EwoudVV/ducktop2/mechanical/layout-planner.html

ducktop2 floorplan

Select Pan Fit - + Save Export Import Reset Panel

Ready

## View

Grid mm Zoom

Snap to grid

Fit Base Fit Lid Fit All

## Selected

Name

X Y Zone

W H Kind

Focus Center H Center V Rotate -45 +45 Duplicate Delete Lock Hide

## Parts

Add Part Select All Clear Front Back

## JSON

Mouse wheel zooms at cursor. Drag empty space to box-select. Spacebar or Pan mode drags the view. Shift/Command-click adds to selection. White handles resize one unlocked part.

## Build Next

Keyboard rev A is now a real 273.5 x 80.0 mm MX ULP daughterboard. Its J320 connector is a Hirose FH12-30S-0.5SH(55), 30-pin 0.5 mm right-angle FFC. Use this planner to freeze the mainboard envelope, side/rear connector zones, thermal stack, battery clearances, display direct-eDP hinge route, recessed Ethernet jack, microphone opening, and cable paths before freezing the main PCB outline.
