EwoudVV/ducktop2/mechanical/case-prototype/viewer-template.html

# ducktop2 / case prototype

Actual CAD geometry. Drag to orbit, scroll to zoom. Editable parameters are in assembly.json.

closed105°180° opening 105° explodedtopsection sidereset view

cut at X off

unresolved fit checks

Framework Computer Inc hinge references: CC BY 4.0, revision 0 / 2023-06-27. STEP coordinates retain front +Y and use Z down; this view is rotated to show height upward.

loading geometry…
