EwoudVV/ducktop2/mechanical/case-prototype/mounting-schedule.csv

reference | X_mm | Y_mm | Z_mm | mating_part | hole_mm | thread | support_height_mm | fastener_length_mm | insulation | status | washer_thickness_mm | top_thread_engagement_mm | engagement_mm | head_diameter_mm | head_height_mm | OEM_screw_length_mm
center/H21 | 110.25 | 6.05 | -6.4 | base, nylon M2.5 male/female standoff | 2.7 | M2.5 | 4.0 | 5 | nylon screw, support, washer and underside nut; preserve PCB isolation | XY/drill verified from saved board; purchased hardware fit pending | 0.5 | 2.9
center/H22 | 105.0 | 70.0 | -6.4 | base, nylon M2.5 male/female standoff | 2.7 | M2.5 | 4.0 | 5 | nylon screw, support, washer and underside nut; preserve PCB isolation | XY/drill verified from saved board; purchased hardware fit pending | 0.5 | 2.9
center/H23 | 124.1 | 180.4 | -6.4 | base, nylon M2.5 male/female standoff | 2.7 | M2.5 | 4.0 | 5 | nylon screw, support, washer and underside nut; preserve PCB isolation | XY/drill verified from saved board; purchased hardware fit pending | 0.5 | 2.9
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
