EwoudVV/ducktop2/keyboard/images/layout.png

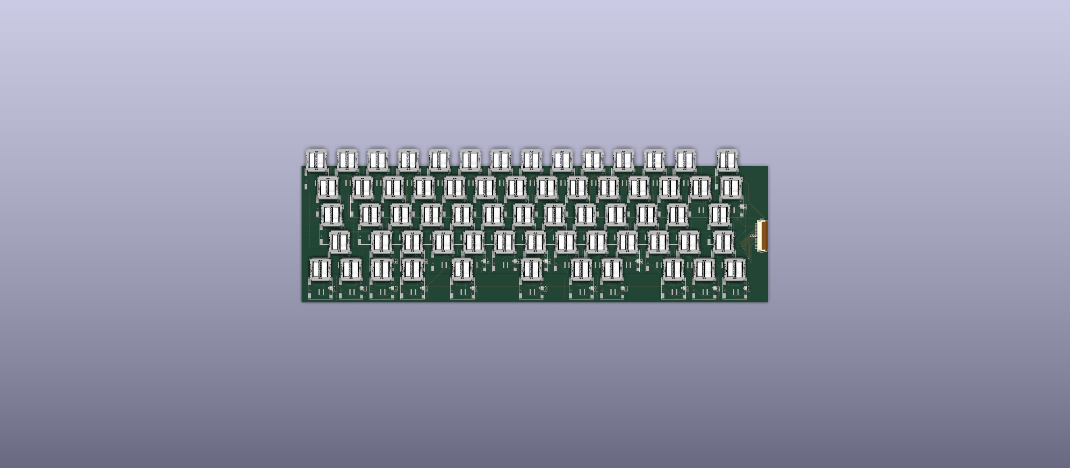
keyboard/images/layout.png
