EwoudVV/ducktop2/mechanical/case-prototype/views/closed.png

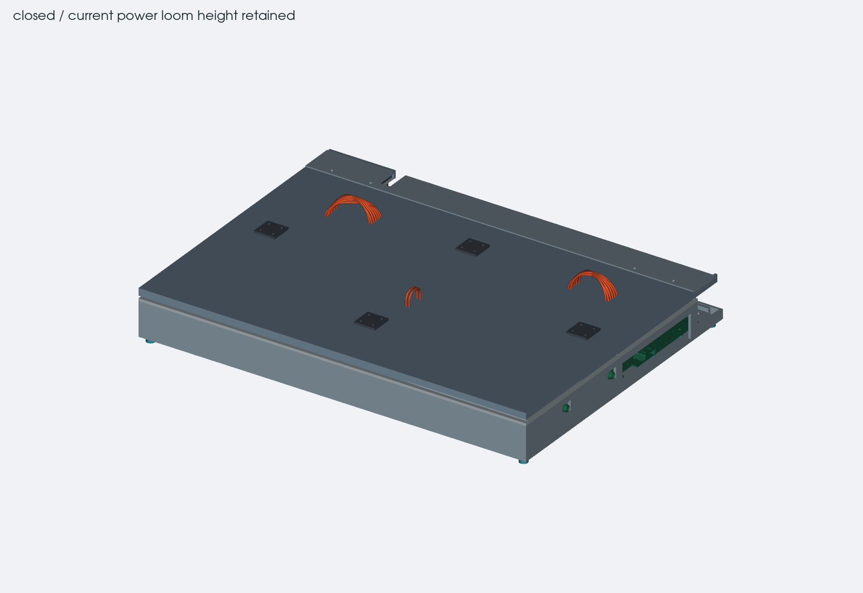
mechanical/case-prototype/views/closed.png
