EwoudVV/ducktop2/mechanical/case-prototype/views/cooling-section.png

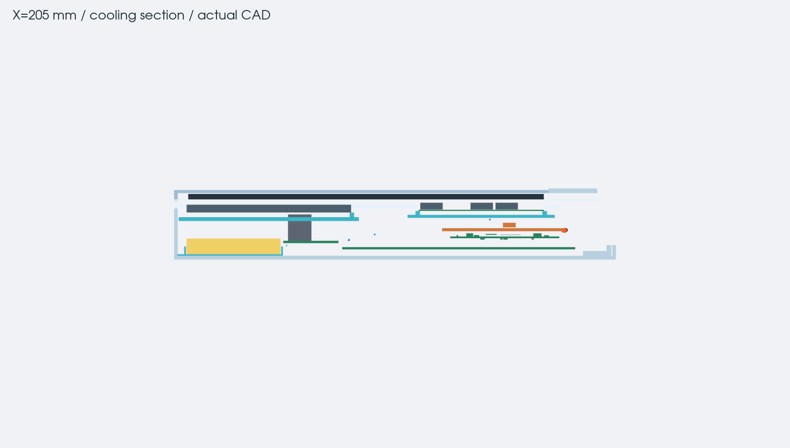
mechanical/case-prototype/views/cooling-section.png
