EwoudVV/ducktop2/mechanical/case-prototype/views/exploded.png

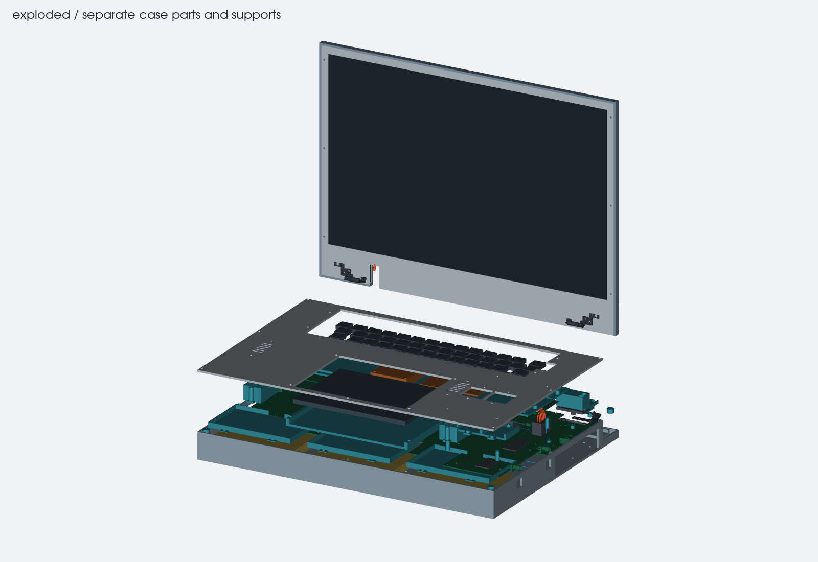
mechanical/case-prototype/views/exploded.png
