EwoudVV/ducktop2/mechanical/case-prototype/views/inside.png

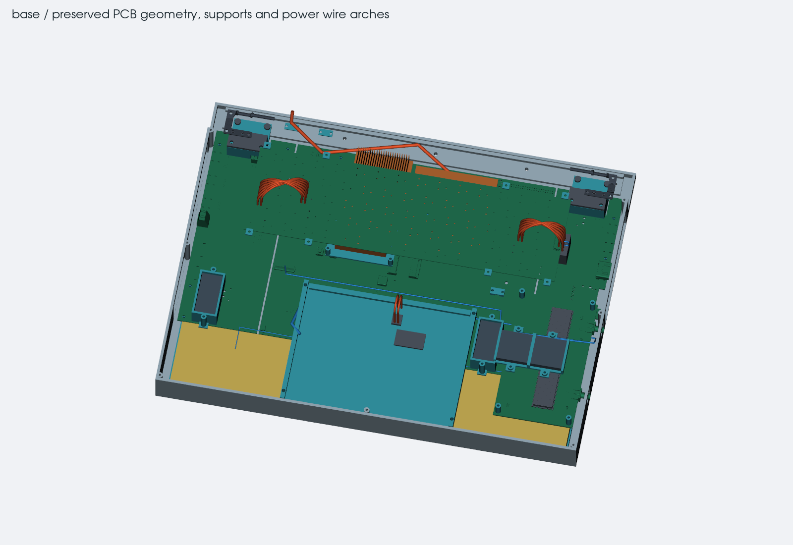
mechanical/case-prototype/views/inside.png
