EwoudVV/ducktop2/mechanical/power-harness.png

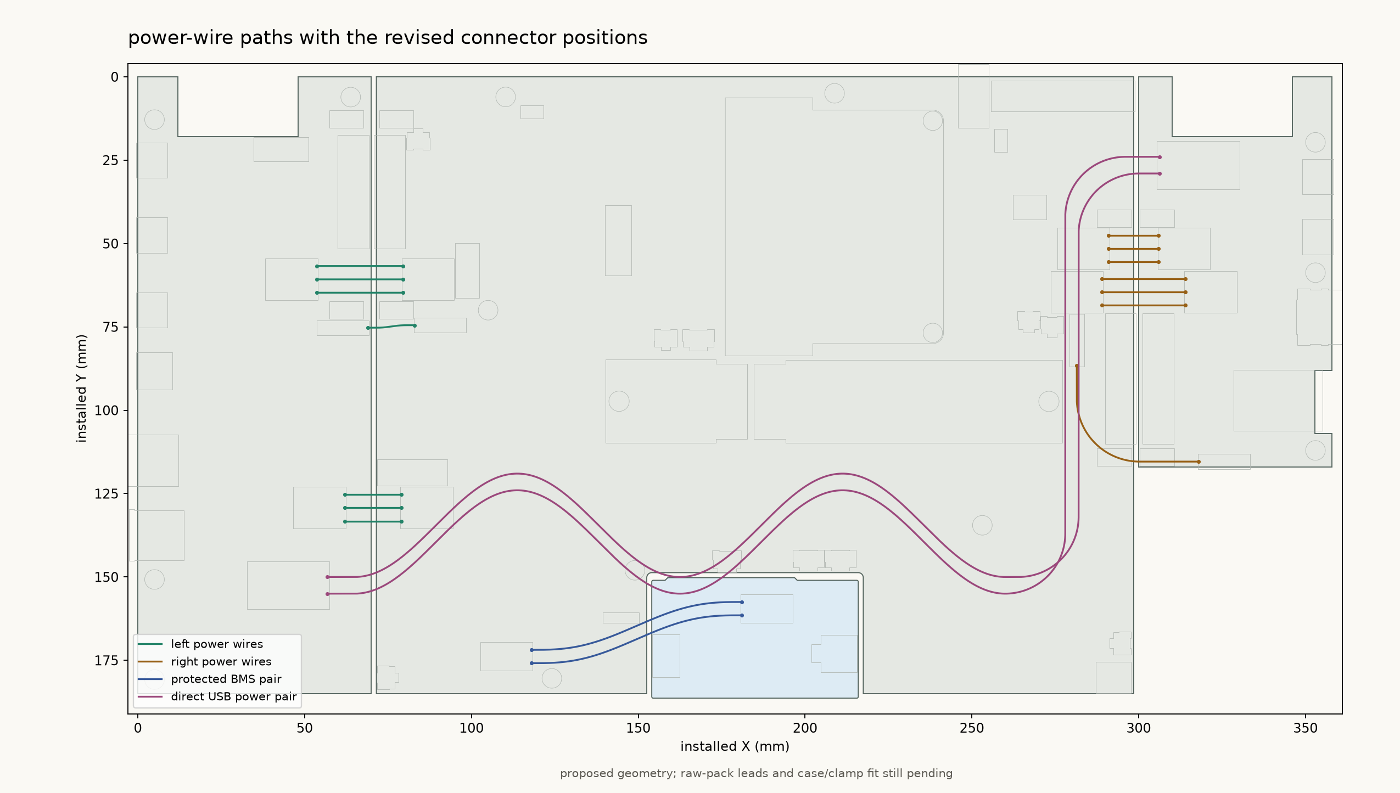
mechanical/power-harness.png
