EwoudVV/ducktop2/radio_daughterboard/images/iso.png

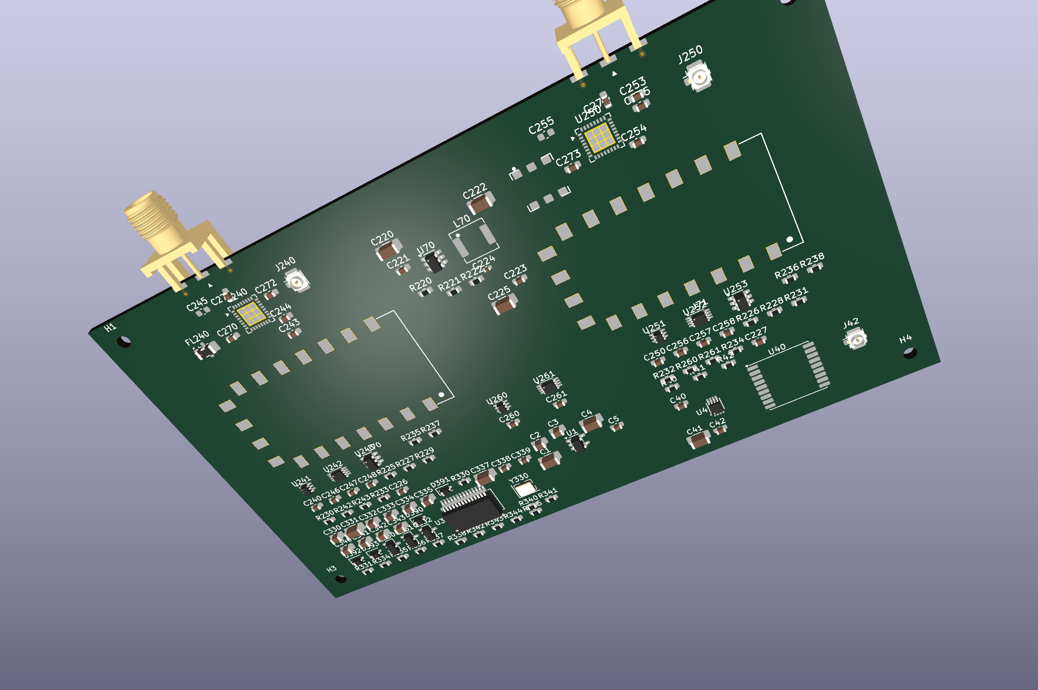
radio_daughterboard/images/iso.png
