EwoudVV/ducktop2/radio_daughterboard/images/top.png

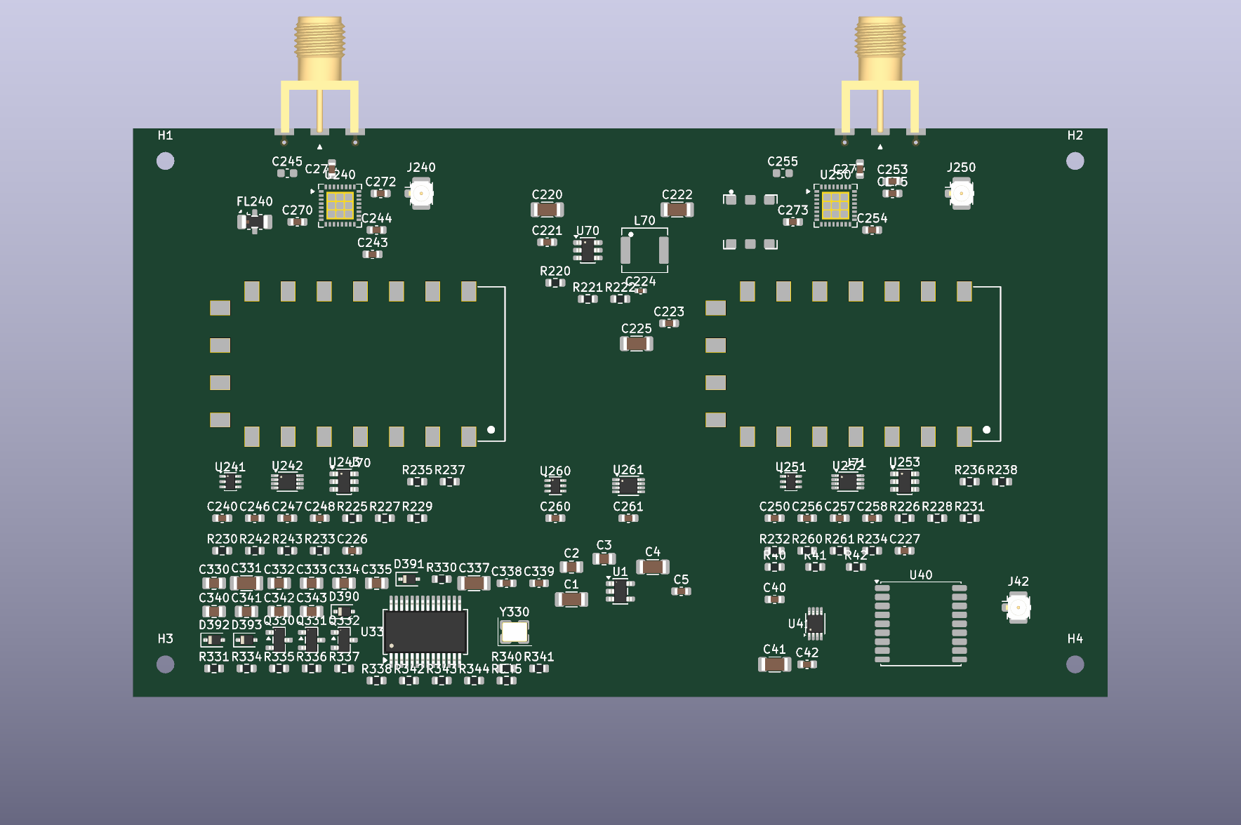
radio_daughterboard/images/top.png
