EwoudVV/ducktop2/mechanical/case-prototype/exports/hinge-tests/right-base-block.stl

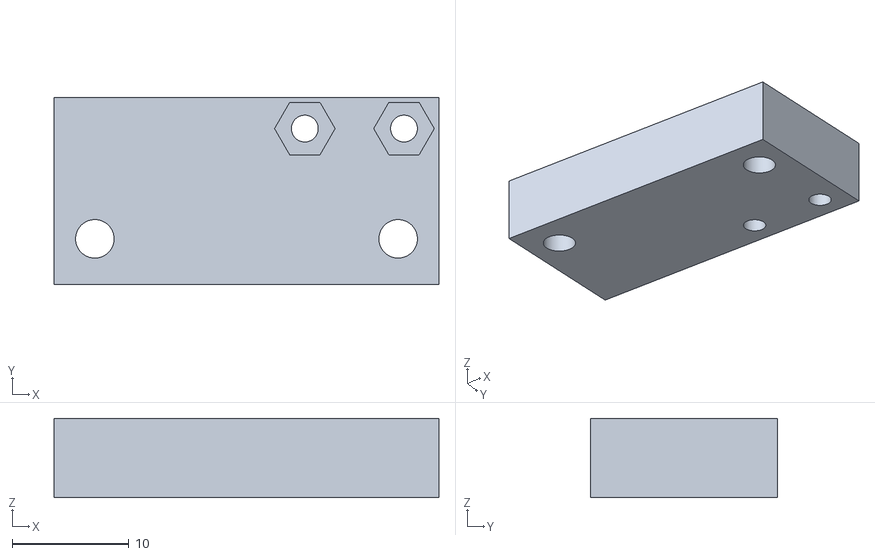
[picture p27: CAD file, 2026-09-26]
mechanical/case-prototype/exports/hinge-tests/right-base-block.stl
33.0 x 16.0 x 6.80
