EwoudVV/ducktop2/mechanical/case-prototype/exports/parts/right-lid-seat-2.step

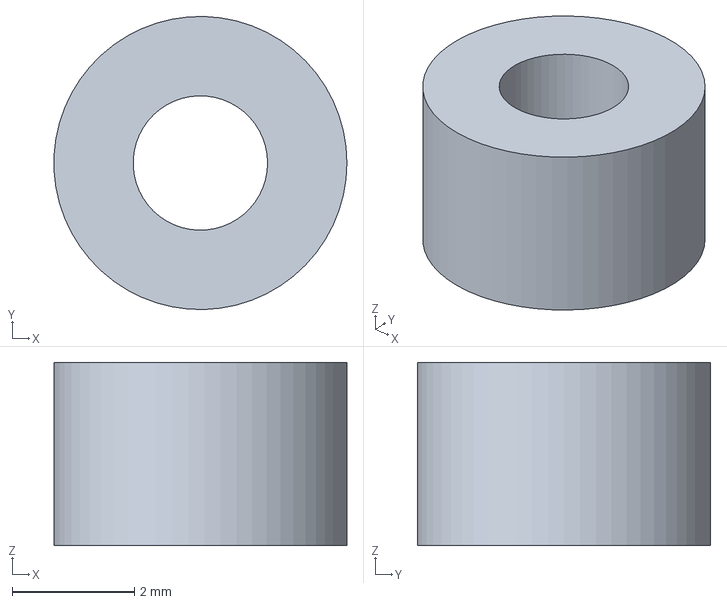
[picture p28: CAD file, 2026-09-26]
mechanical/case-prototype/exports/parts/right-lid-seat-2.step
4.80 x 4.80 x 3.00 mm
