EwoudVV/ducktop2/mechanical/case-prototype/exports/hinge-tests/left-base-block.stl

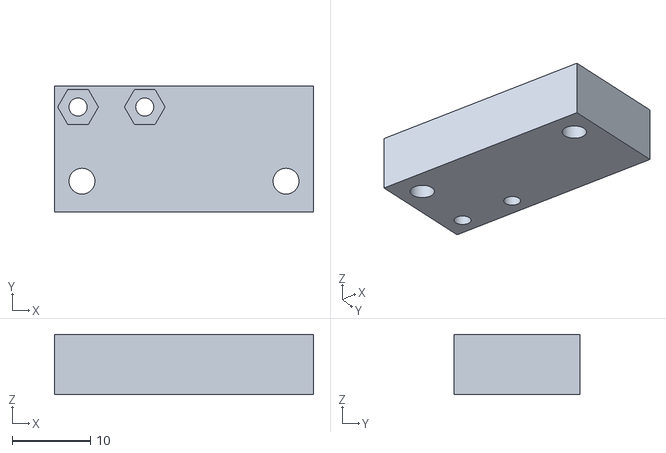
[picture p29: CAD file, 2026-09-26]
mechanical/case-prototype/exports/hinge-tests/left-base-block.stl
33.0 x 16.0 x 7.70
