EwoudVV/ducktop2/mechanical/case-prototype/exports/parts/cable-clamp-3.step

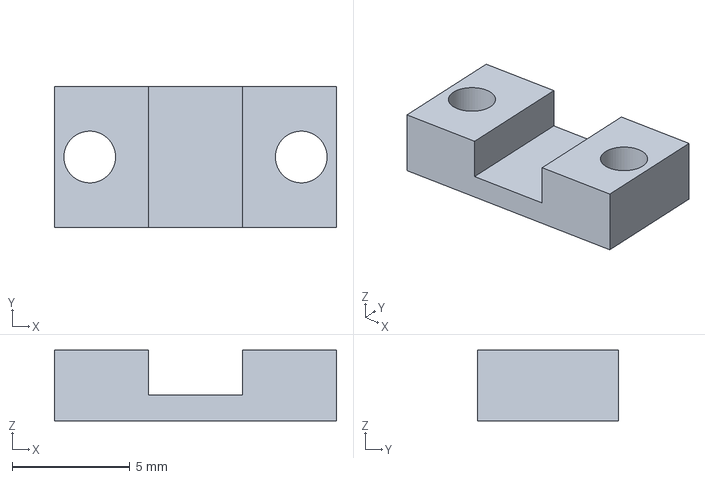
[picture p30: CAD file, 2026-09-26]
mechanical/case-prototype/exports/parts/cable-clamp-3.step
12.0 x 6.00 x 3.00 mm
