EwoudVV/ducktop2/mechanical/case-prototype/exports/parts/lid-shell-21.step

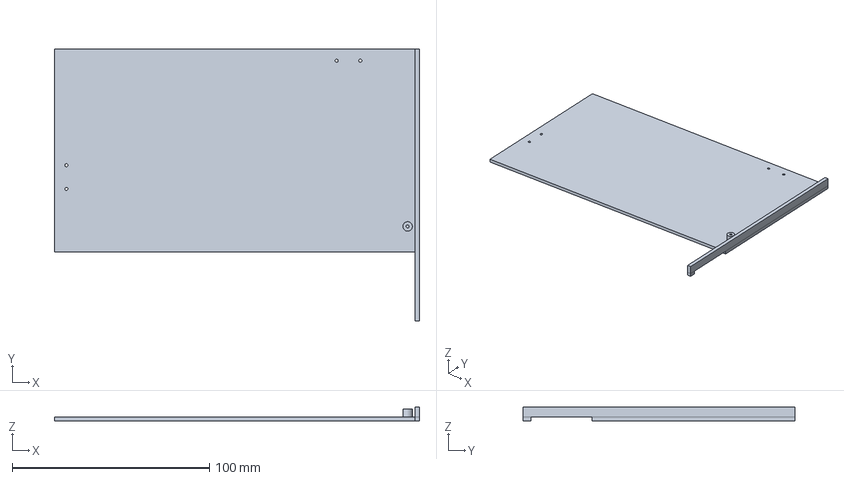
[picture p31: CAD file, 2026-09-26]
mechanical/case-prototype/exports/parts/lid-shell-21.step
185.0 x 138.0 x 7.00 mm
