EwoudVV/ducktop2/mechanical/case-prototype/exports/parts/deck-21.step

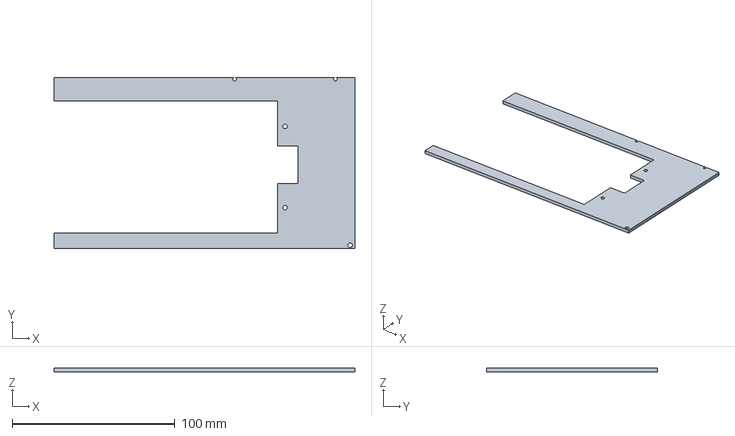
[picture p32: CAD file, 2026-09-26]
mechanical/case-prototype/exports/parts/deck-21.step
185.0 x 105.0 x 2.40 mm
