EwoudVV/ducktop2/mechanical/case-prototype/exports/parts/bezel-22.step

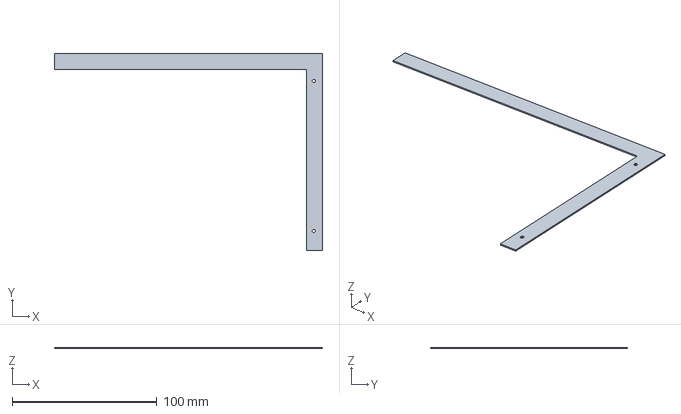
[picture p33: CAD file, 2026-09-26]
mechanical/case-prototype/exports/parts/bezel-22.step
185.0 x 136.0 x 0.8 mm
