EwoudVV/ducktop2/mechanical/case-prototype/exports/parts/rear-spine-fit-only-1.stl

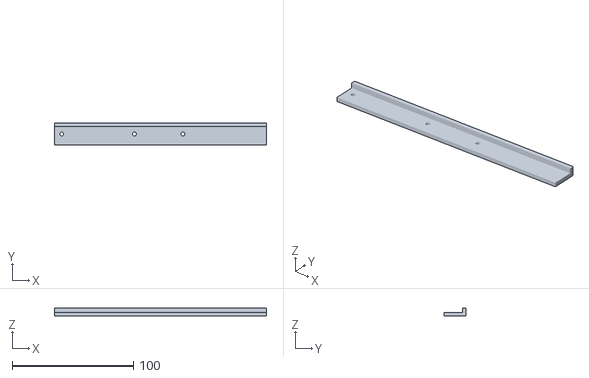
[picture p34: CAD file, 2026-09-26]
mechanical/case-prototype/exports/parts/rear-spine-fit-only-1.stl
175.0 x 18.0 x 6.60
