EwoudVV/ducktop2/mechanical/case-prototype/exports/parts/speaker-2-cup.step

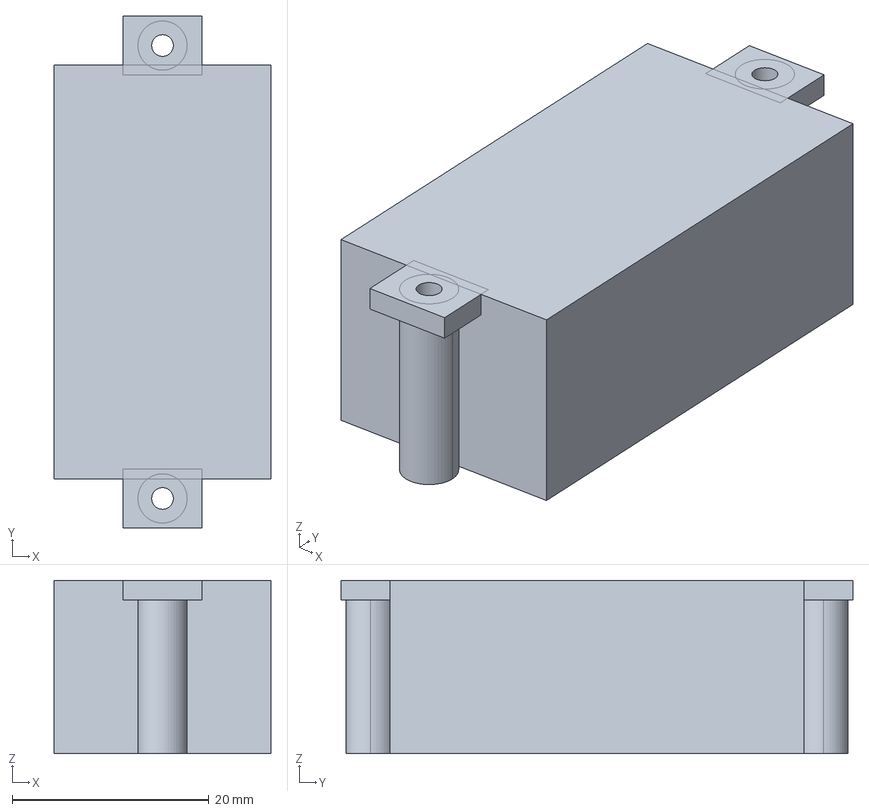
[picture p35: CAD file, 2026-09-26]
mechanical/case-prototype/exports/parts/speaker-2-cup.step
22.0 x 52.0 x 17.6 mm
