EwoudVV/ducktop2/mechanical/case-prototype/exports/parts/right-hinge-tower.step

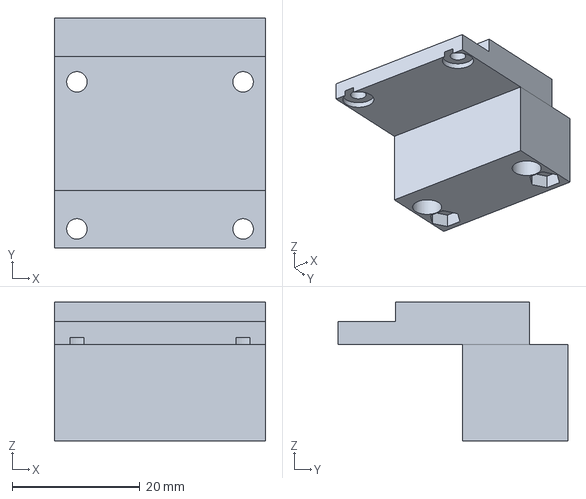
[picture p36: CAD file, 2026-09-26]
mechanical/case-prototype/exports/parts/right-hinge-tower.step
33.0 x 36.0 x 21.7 mm
