EwoudVV/ducktop2/mechanical/case-prototype/exports/parts/base-21.step

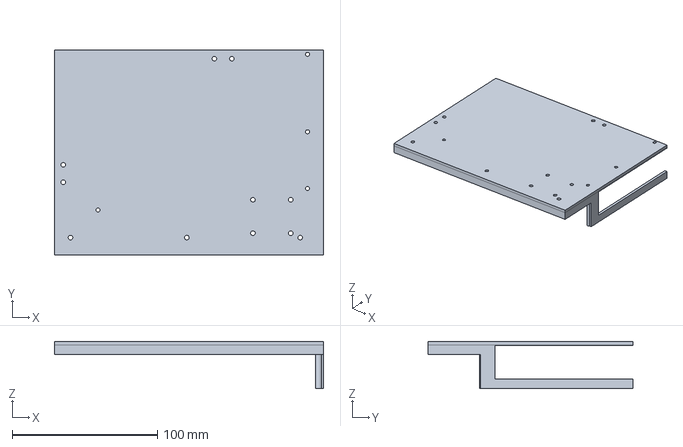
[picture p37: CAD file, 2026-09-26]
mechanical/case-prototype/exports/parts/base-21.step
185.0 x 141.0 x 32.6 mm
