EwoudVV/ducktop2/mechanical/case-prototype/exports/parts/rear-spine.step

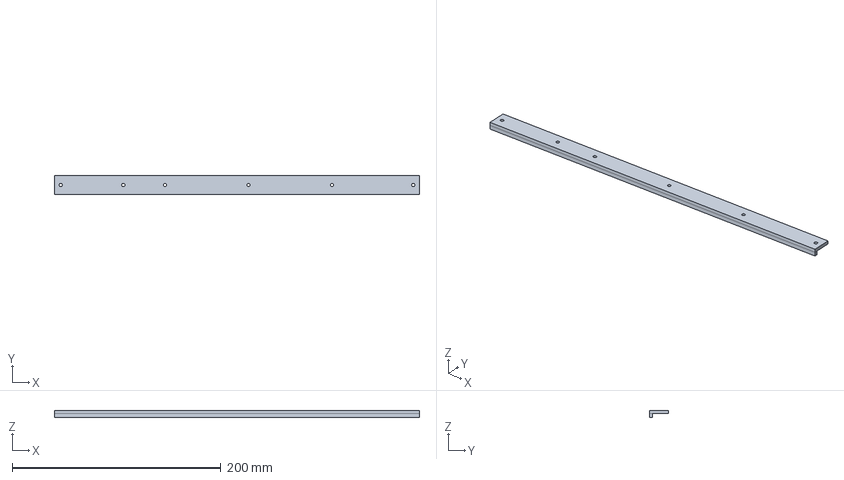
[picture p38: CAD file, 2026-09-26]
mechanical/case-prototype/exports/parts/rear-spine.step
350.0 x 18.0 x 6.60 mm
