EwoudVV/ducktop2/mechanical/case-prototype/exports/parts/bezel-11.step

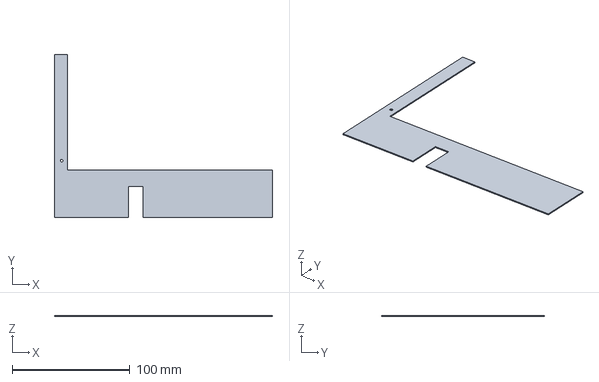
[picture p39: CAD file, 2026-09-26]
mechanical/case-prototype/exports/parts/bezel-11.step
185.0 x 138.0 x 0.8 mm
