EwoudVV/ducktop2/mechanical/case-prototype/exports/parts/left-hinge-tower.step

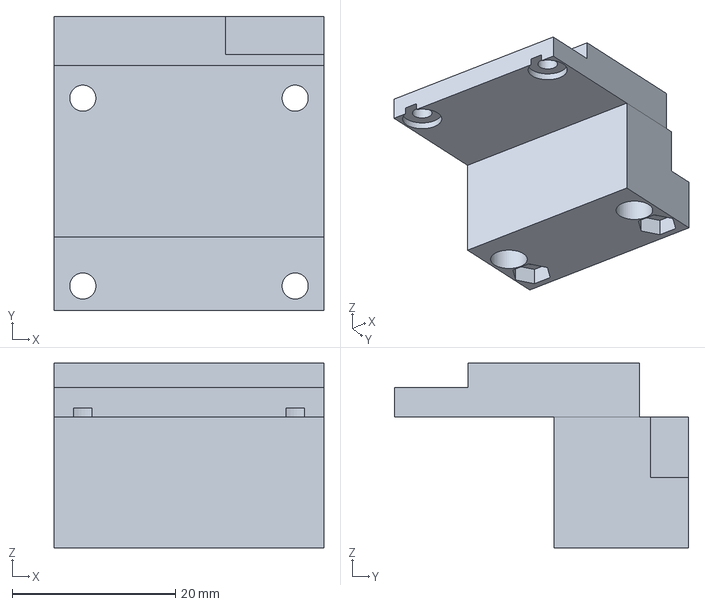
[picture p41: CAD file, 2026-09-26]
mechanical/case-prototype/exports/parts/left-hinge-tower.step
33.0 x 36.0 x 22.6 mm
