EwoudVV/ducktop2/mechanical/case-prototype/exports/parts/base-12.step

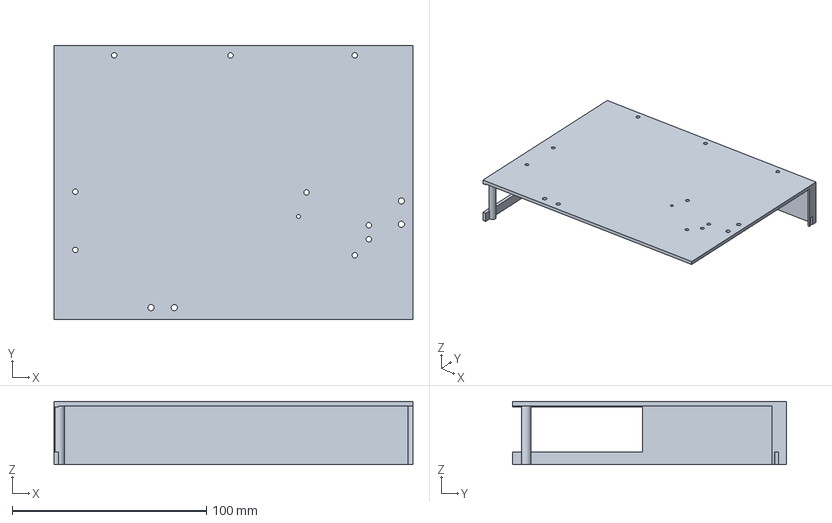
[picture p43: CAD file, 2026-09-26]
mechanical/case-prototype/exports/parts/base-12.step
185.0 x 141.0 x 32.6 mm
