EwoudVV/ducktop2/mechanical/case-prototype/exports/parts/keyboard-carrier-21.step

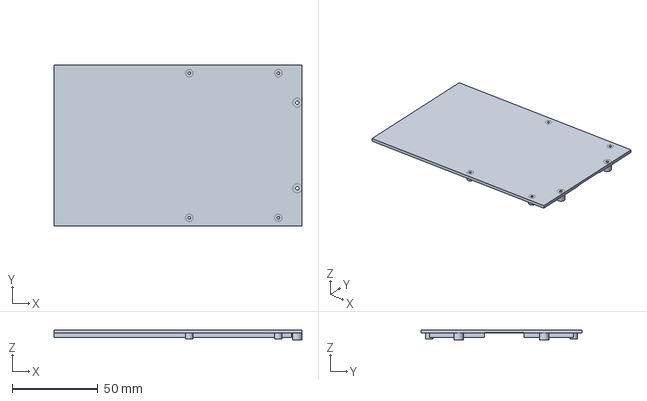
[picture p44: CAD file, 2026-09-26]
mechanical/case-prototype/exports/parts/keyboard-carrier-21.step
144.8 x 94.0 x 6.10 mm
