EwoudVV/ducktop2/mechanical/case-prototype/exports/parts/lid-cross-rail-fit-only-1.stl

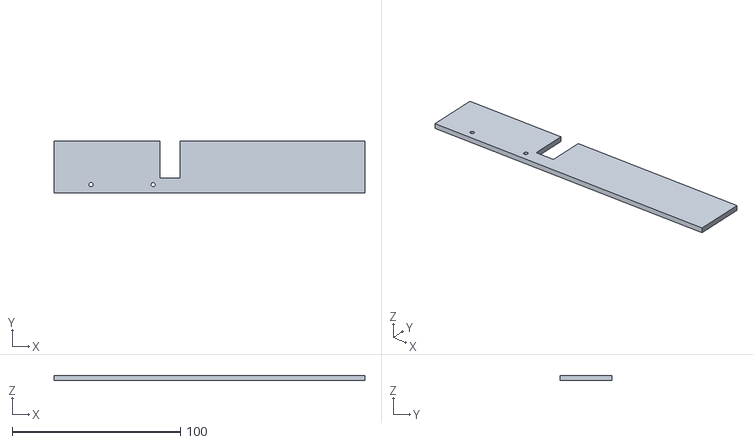
[picture p45: CAD file, 2026-09-26]
mechanical/case-prototype/exports/parts/lid-cross-rail-fit-only-1.stl
185.0 x 31.0 x 3.00
