EwoudVV/ducktop2/mechanical/case-prototype/exports/parts/blower-fit-cradle.step

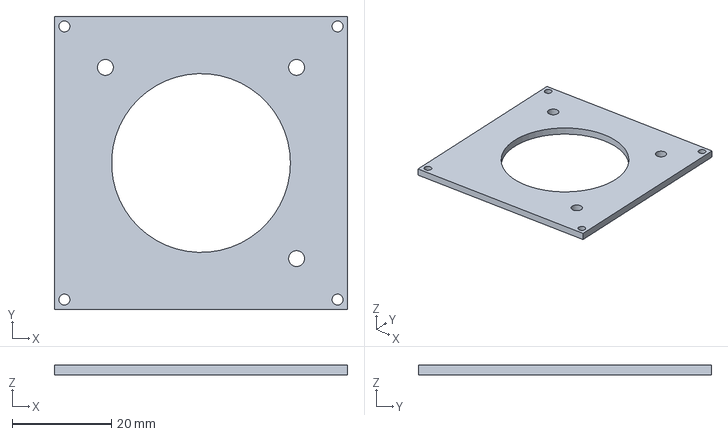
[picture p46: CAD file, 2026-09-26]
mechanical/case-prototype/exports/parts/blower-fit-cradle.step
59.0 x 59.0 x 2.00 mm
