EwoudVV/ducktop2/mechanical/case-prototype/exports/parts/oled-2-clip-tray.step

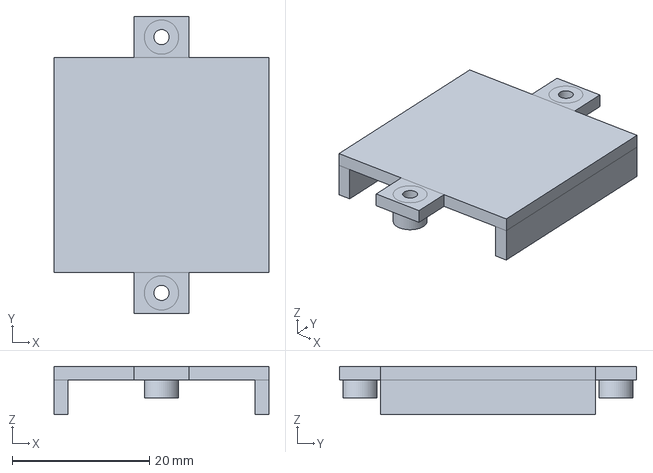
[picture p47: CAD file, 2026-09-26]
mechanical/case-prototype/exports/parts/oled-2-clip-tray.step
31.3 x 43.3 x 7.00 mm
