EwoudVV/ducktop2/mechanical/case-prototype/exports/parts/lid-shell-12.step

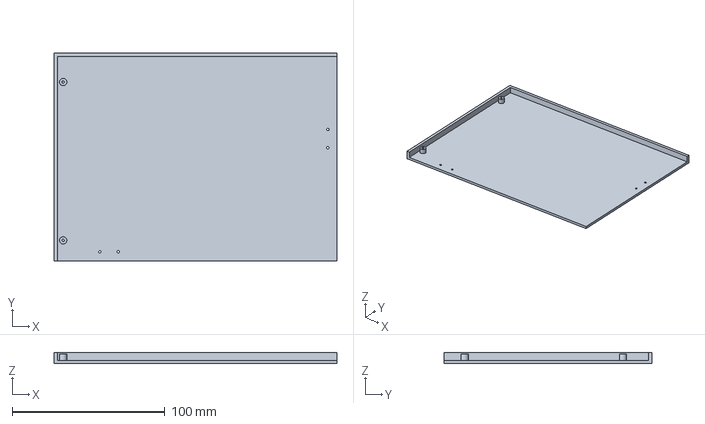
[picture p48: CAD file, 2026-09-26]
mechanical/case-prototype/exports/parts/lid-shell-12.step
185.0 x 136.0 x 7.00 mm
