EwoudVV/ducktop2/mechanical/case-prototype/exports/parts/cable-clamp-1-pedestal.step

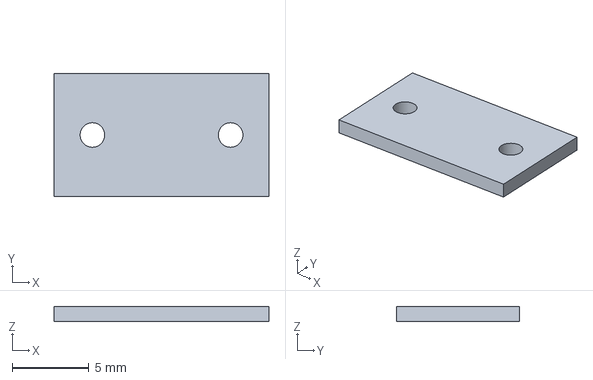
[picture p49: CAD file, 2026-09-26]
mechanical/case-prototype/exports/parts/cable-clamp-1-pedestal.step
14.0 x 8.00 x 1.00 mm
