EwoudVV/ducktop2/mechanical/case-prototype/exports/parts/left-lid-steel-plate.step

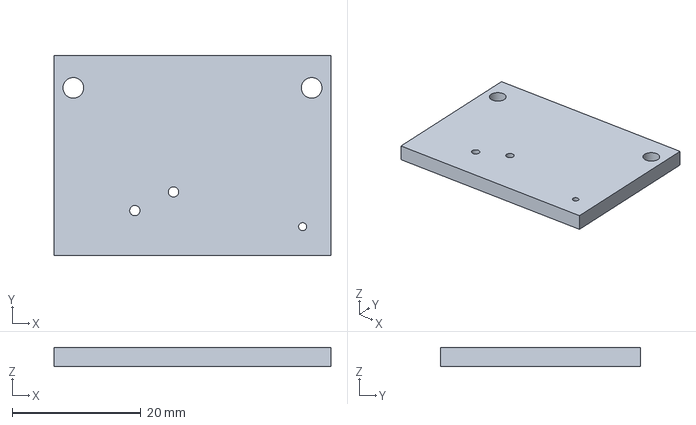
[picture p50: CAD file, 2026-09-26]
mechanical/case-prototype/exports/parts/left-lid-steel-plate.step
43.0 x 31.0 x 3.00 mm
