EwoudVV/ducktop2/mechanical/case-prototype/exports/parts/deck-11.step

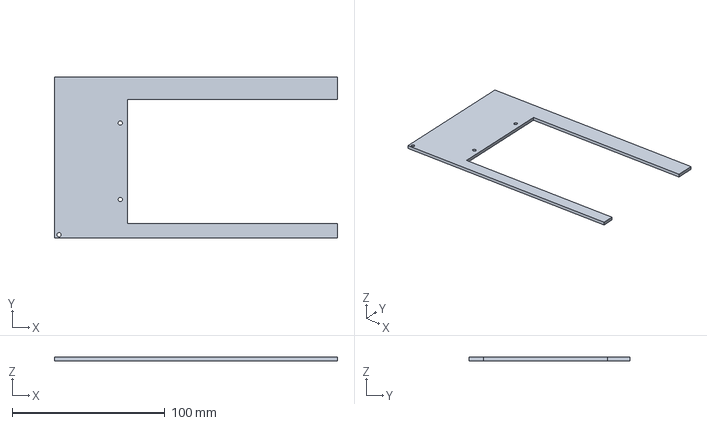
[picture p51: CAD file, 2026-09-26]
mechanical/case-prototype/exports/parts/deck-11.step
185.0 x 105.0 x 2.40 mm
