EwoudVV/ducktop2/mechanical/case-prototype/exports/parts/lid-cross-rail.step

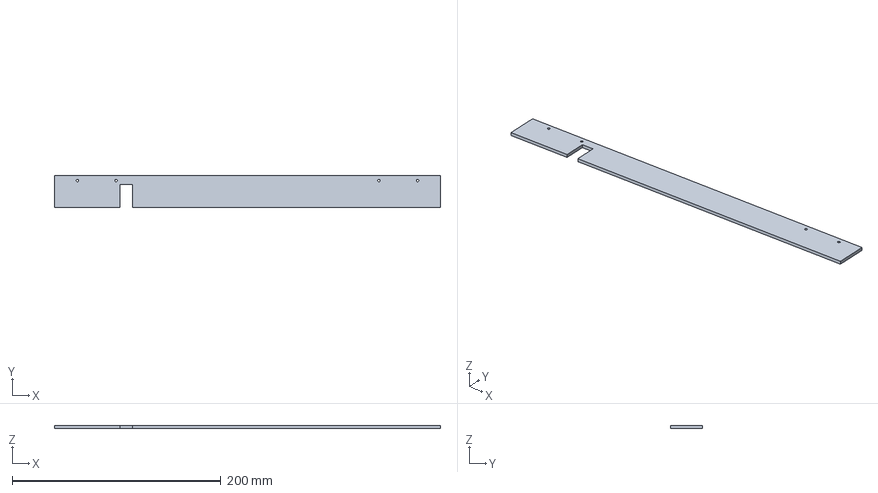
[picture p52: CAD file, 2026-09-26]
mechanical/case-prototype/exports/parts/lid-cross-rail.step
370.0 x 31.0 x 3.00 mm
