EwoudVV/ducktop2/mechanical/case-prototype/exports/parts/trackpad-bridge.step

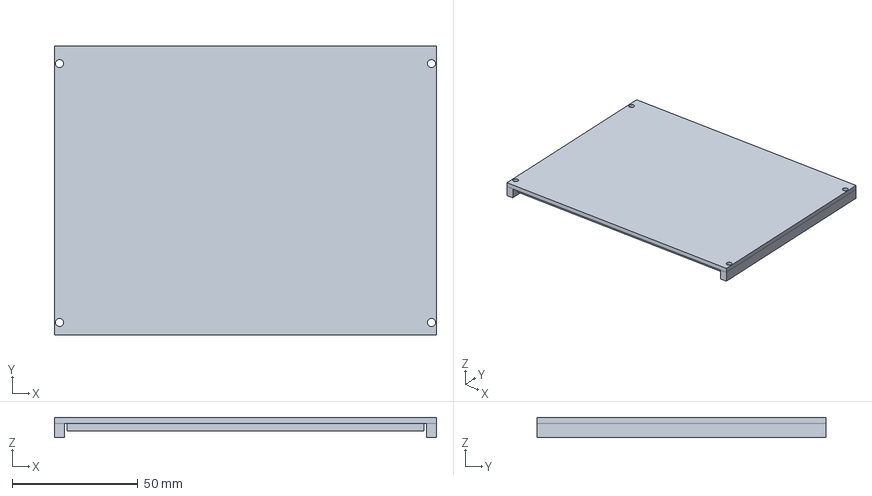
[picture p53: CAD file, 2026-09-26]
mechanical/case-prototype/exports/parts/trackpad-bridge.step
152.0 x 115.0 x 8.10 mm
