EwoudVV/ducktop2/mechanical/case-prototype/exports/parts/base-22.step

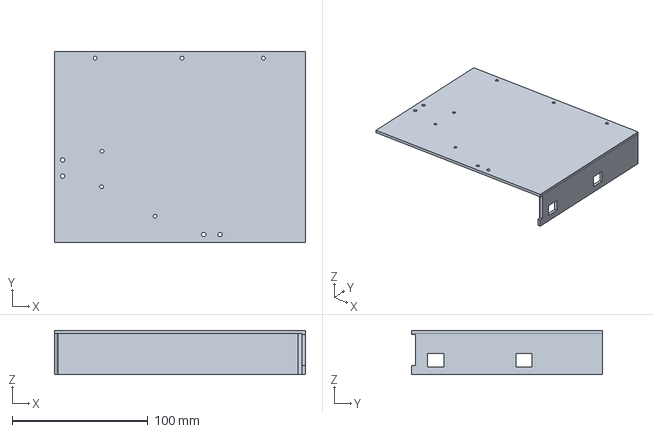
[picture p54: CAD file, 2026-09-26]
mechanical/case-prototype/exports/parts/base-22.step
185.0 x 141.0 x 32.6 mm
