EwoudVV/ducktop2/mechanical/case-prototype/exports/parts/deck-22.step

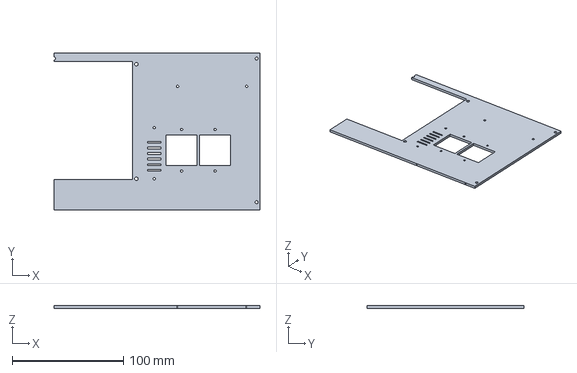
[picture p55: CAD file, 2026-09-26]
mechanical/case-prototype/exports/parts/deck-22.step
185.0 x 141.0 x 2.40 mm
