EwoudVV/ducktop2/manufacturing/bms/back.png

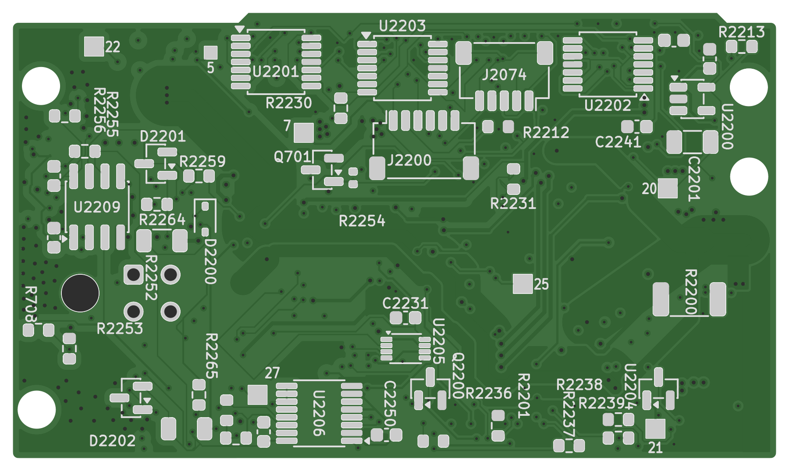
manufacturing/bms/back.png
