EwoudVV/ducktop2/manufacturing/bms/front.png

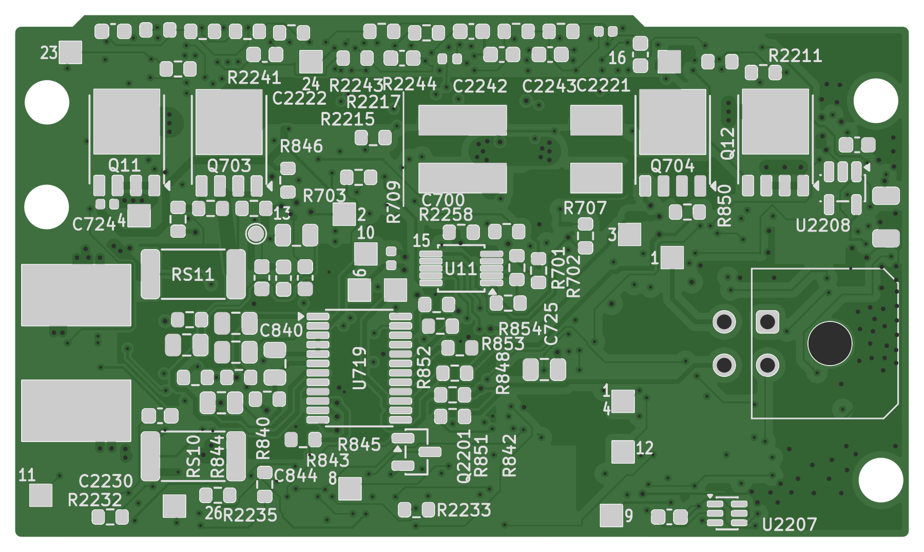
manufacturing/bms/front.png
