EwoudVV/ducktop2/firmware/ec_target/tusb_config.h

#ifndef DUCKTOP2_TUSB_CONFIG_H
#define DUCKTOP2_TUSB_CONFIG_H

#define CFG_TUSB_MCU OPT_MCU_STM32F4
#define CFG_TUSB_OS OPT_OS_NONE
#define CFG_TUSB_DEBUG 0
#define CFG_TUSB_RHPORT0_MODE (OPT_MODE_DEVICE | OPT_MODE_FULL_SPEED)
#define CFG_TUD_ENABLED 1
#define CFG_TUH_ENABLED 0
#define CFG_TUD_MAX_SPEED OPT_MODE_FULL_SPEED
#define CFG_TUD_ENDPOINT0_SIZE 64
#define CFG_TUD_HID 3
#define CFG_TUD_HID_EP_BUFSIZE 64
#define CFG_TUD_TASK_QUEUE_SZ 32
#define CFG_TUD_DWC2_SLAVE_ENABLE 1
#define CFG_TUD_DWC2_DMA_ENABLE 0
/* The physical VBUS-valid circuit controls the external USB switch. */
#define CFG_TUD_VBUS_DETECT_HW 0

#endif
