EwoudVV/ducktop2/gen/verify_design_contracts.py

#!/usr/bin/env python3
"""Ducktop2 high-risk design contract checks.

This complements KiCad ERC/DRC.  It asserts project-specific wiring decisions
that generic electrical rules cannot know, especially around battery entry,
USB-C power, OLED module pin order, and main-PCB footprint staging.
"""

from __future__ import annotations

import argparse
import copy
import json
import re
import subprocess
import sys
import xml.etree.ElementTree as ET
from pathlib import Path

import sync_main_pcb_from_netlist as sync
from part_identity import identity_errors


ROOT = Path(__file__).resolve().parents[1]
PCB = ROOT / "ducktop2-center.kicad_pcb"
CURRENT_DRC = ROOT / "verification" / "generated" / "contract_drc_current.json"


class CheckFailure(RuntimeError):
    pass


def fail(msg: str) -> None:
    raise CheckFailure(msg)


def expect(got: str | None, want: str, label: str) -> None:
    if got != want:
        fail(f"{label}: expected {want!r}, got {got!r}")


def expect_prefix(got: str | None, prefix: str, label: str) -> None:
    if got is None or not got.startswith(prefix):
        fail(f"{label}: expected prefix {prefix!r}, got {got!r}")


def expect_contains(got: str | None, needle: str, label: str) -> None:
    if got is None or needle not in got:
        fail(f"{label}: expected to contain {needle!r}, got {got!r}")


def comp(components, ref):
    item = components.get(ref)
    if item is None:
        fail(f"missing schematic component {ref}")
    return item


def net(components, ref, pin):
    return comp(components, ref).pin_nets.get(pin)


def prop(components, ref, name):
    return comp(components, ref).properties.get(name)


def local_net(sheet: str, name: str) -> str:
    return "/" + sheet.replace("/", "{slash}") + "/" + name


def expect_unconnected(components, ref: str, pin: str) -> None:
    got = net(components, ref, pin)
    # Native XML carries one symbol UUID per unit. A single-unit connector
    # cannot acquire a suffix just because its net name contains one.
    units = len(getattr(comp(components, ref), 'unit_paths', ())) or len(getattr(comp(components, ref), 'path', '').split()) or 1
    suffix = f"(?:[{'ABCDEFGHIJKLMNOPQRSTUVWXYZ'[:units]}])?" if 1 < units <= 26 else ""
    pattern = rf"unconnected-\({re.escape(ref)}{suffix}(?:-[^()]*)?-Pad{re.escape(pin)}\)"
    if got is None or re.fullmatch(pattern, got) is None:
        fail(f"{ref} pin {pin}: expected an exact KiCad unconnected net, got {got!r}")
    nodes = {(other_ref, other_pin) for other_ref, item in components.items()
             for other_pin, other_net in item.pin_nets.items() if other_net == got}
    if nodes != {(ref, pin)}:
        fail(f"{ref} pin {pin}: no-connect net is shared by {sorted(nodes)}")


def expect_value_prefix(components, ref: str, prefix: str, label: str | None = None) -> None:
    expect_prefix(comp(components, ref).value, prefix, label or f"{ref} value")


def component_flags(project: str = "ducktop2") -> tuple[set[str], set[str]]:
    _sch, netlist = sync.PROJECTS[project]
    root = ET.parse(netlist).getroot()
    dnp: set[str] = set()
    exclude_bom: set[str] = set()
    for node in root.findall(".//comp"):
        ref = node.get("ref") or ""
        props = {p.get("name") for p in node.findall("property")}
        if "dnp" in props:
            dnp.add(ref)
        if "exclude_from_bom" in props:
            exclude_bom.add(ref)
    return dnp, exclude_bom


def component_pin_names(netlist: Path | None = None) -> dict[tuple[str, str], str]:
    """Return the library-declared pin name for every instantiated pin."""
    root = ET.parse(netlist if netlist is not None else sync.NETLIST).getroot()
    library_pins: dict[tuple[str, str], dict[str, str]] = {}
    for libpart in root.findall(".//libpart"):
        key = (libpart.get("lib") or "", libpart.get("part") or "")
        library_pins[key] = {
            pin.get("num") or "": pin.get("name") or ""
            for pin in libpart.findall("./pins/pin")
        }
    result: dict[tuple[str, str], str] = {}
    for node in root.findall(".//comp"):
        ref = node.get("ref") or ""
        source = node.find("libsource")
        if source is None:
            continue
        key = (source.get("lib") or "", source.get("part") or "")
        for pin, name in library_pins.get(key, {}).items():
            result[(ref, pin)] = name
    return result


def net_nodes() -> dict[str, set[tuple[str, str]]]:
    root = ET.parse(sync.NETLIST).getroot()
    return {
        node.get("name") or "": {
            (item.get("ref") or "", item.get("pin") or "")
            for item in node.findall("node")
        }
        for node in root.findall(".//net")
    }


def check_tps2553_semantics(components, pin_names) -> None:
    expected = {
        "1": ("IN", "/SYS_5V"),
        "2": ("GND", "GND"),
        "3": ("EN", "/MU_HOST_ACTIVE"),
        "4": ("~{FAULT}", "/INTERNAL_USB_VBUS_FAULT_N"),
        "5": ("ILIM", "/Mu Carrier/INTERNAL_USB_VBUS_ILIM"),
        "6": ("OUT", "/Mu Carrier/INTERNAL_USB_VBUS"),
    }
    for pin, (name, expected_net) in expected.items():
        expect(pin_names.get(("U770", pin)), name, f"U770 physical pin {pin} function")
        expect(net(components, "U770", pin), expected_net,
               f"U770 {name} physical pin {pin} net")


def self_test_tps2553_guard(components, pin_names) -> None:
    """Prove the semantic guard rejects the exact OUT/ILIM regression."""
    swapped = dict(components)
    bad = copy.copy(comp(components, "U770"))
    bad.pin_nets = dict(bad.pin_nets)
    bad.pin_nets["5"], bad.pin_nets["6"] = bad.pin_nets["6"], bad.pin_nets["5"]
    swapped["U770"] = bad
    try:
        check_tps2553_semantics(swapped, pin_names)
    except CheckFailure:
        return
    fail("TPS2553 negative fixture did not reject swapped OUT/ILIM nets")


def footprint_map():
    text = PCB.read_text(encoding="utf-8")
    return {fp.ref: fp for fp in sync.footprints(text)}, text


def at_tuple(block: str):
    m = re.search(r'\n\s*\(at\s+([-0-9.]+)\s+([-0-9.]+)(?:\s+([-0-9.]+))?\)', block)
    if not m:
        fail("footprint is missing top-level at")
    return float(m.group(1)), float(m.group(2)), float(m.group(3) or 0.0)


def source_footprint_pads(path: Path) -> list[tuple[str, float, float, float | None]]:
    """Return named/unnamed source-footprint pad coordinates and drill sizes."""
    text = path.read_text(encoding="utf-8")
    pads: list[tuple[str, float, float, float | None]] = []
    for _, _, block in sync.iter_blocks(text, "(pad "):
        at = re.search(r'\(at\s+([-0-9.]+)\s+([-0-9.]+)', block)
        if not at:
            fail(f"{path.name}: pad is missing an at coordinate")
        drill = re.search(r'\(drill\s+([-0-9.]+)', block)
        pads.append(
            (
                sync.pad_name(block),
                float(at.group(1)),
                float(at.group(2)),
                float(drill.group(1)) if drill else None,
            )
        )
    return pads


def rounded_pad_set(pads: list[tuple[str, float, float, float | None]]):
    rounded = [
        (name, round(x, 3), round(y, 3), None if drill is None else round(drill, 3))
        for name, x, y, drill in pads
    ]
    return sorted(
        rounded,
        key=lambda item: (item[0], item[1], item[2], -1.0 if item[3] is None else item[3]),
    )


def check_custom_footprint_sources() -> None:
    m2_standoff_path = (
        ROOT / "ducktop2.pretty" /
        "SMT_Standoff_M2_H2.5_C4_Tail2.7x1.5.kicad_mod"
    )
    m2_standoff_text = m2_standoff_path.read_text(encoding="utf-8")
    m2_standoff_pads = rounded_pad_set(source_footprint_pads(m2_standoff_path))
    expected_m2_standoff_pads = rounded_pad_set([
        ("1", 0.0, 0.0, 2.75),
        ("1", 0.0, 0.0, None),
    ])
    if m2_standoff_pads != expected_m2_standoff_pads:
        fail(
            "M.2 standoff source pads differ from the LattePanda V2 land "
            f"pattern: {m2_standoff_pads}"
        )
    expect_contains(m2_standoff_text, "M2XC4X2.5+C2.7X1.5",
                    "M.2 standoff official source designation")
    if "MDT420STD001" in m2_standoff_text:
        fail("M.2 standoff footprint must not cite incompatible MDT420STD001")

    aux_fet_path = ROOT / "ducktop2.pretty" / "CSD19537Q3_DQG.kicad_mod"
    aux_fet_text = aux_fet_path.read_text(encoding="utf-8")
    aux_fet_expected = [
        ("1", -1.44, -0.975, None),
        ("2", -1.44, -0.325, None),
        ("3", -1.44, 0.325, None),
        ("4", -1.44, 0.975, None),
        ("5", 0.385, 0.0, None),
    ]
    named_aux_fet_pads = [
        pad for pad in source_footprint_pads(aux_fet_path) if pad[0]
    ]
    if rounded_pad_set(named_aux_fet_pads) != rounded_pad_set(aux_fet_expected):
        fail("CSD19537Q3 source footprint pad centers changed")
    for required in (
        'TI CSD19537Q3, DQG VSON-CLIP 3.3x3.3 mm',
        '(xy 1.371 -0.72)',
        '(size 0.63 0.5)',
    ):
        if required not in aux_fet_text:
            fail(f"CSD19537Q3 source footprint is missing {required}")

    jack_path = ROOT / "ducktop2.pretty" / "JXD1-1022NL_MidMount.kicad_mod"
    jack_text = jack_path.read_text(encoding="utf-8")
    jack_expected: list[tuple[str, float, float, float | None]] = []
    for pin in range(1, 13):
        jack_expected.append(
            (str(pin), 1.27 * (pin - 1), 0.0 if pin % 2 else -1.27, 0.91)
        )
    jack_expected.extend(
        [
            ("13", 14.51, 15.70, 1.02),
            ("14", 14.51, 18.24, 1.02),
            ("15", -0.53, 15.70, 1.02),
            ("16", -0.53, 18.24, 1.02),
            ("SH", -1.80, 4.42, 2.03),
            ("SH", 15.78, 6.76, 1.40),
            ("SH", -1.80, 11.13, 1.40),
            ("SH", 15.78, 13.21, 2.03),
        ]
    )
    if rounded_pad_set(source_footprint_pads(jack_path)) != rounded_pad_set(jack_expected):
        fail("JXD1-1022NL source footprint pin/stake coordinates or drills changed")
    for required in (
        '(fp_rect (start -1.8 -3.25) (end 15.78 22.81)',
        '(fp_line (start -1.8 20.78) (end 15.78 20.78)',
        '(pad "SH" thru_hole oval (at 15.78 13.21) (size 4 2.5) (drill 2.03)',
        '(attr through_hole)',
    ):
        if required not in jack_text:
            fail(f"JXD1-1022NL source footprint is missing {required}")

    mic_path = ROOT / "ducktop2.pretty" / "Infineon_IM68A130V01.kicad_mod"
    mic_text = mic_path.read_text(encoding="utf-8")
    named_mic_pads = [pad for pad in source_footprint_pads(mic_path) if pad[0]]
    mic_expected = [
        ("1", -1.09, 0.775, None),
        ("2", -1.09, 0.0, None),
        ("3", -1.09, -0.775, None),
        ("4", 0.575, -0.64, None),
    ]
    if rounded_pad_set(named_mic_pads) != rounded_pad_set(mic_expected):
        fail("IM68A130 source footprint electrical-pad coordinates changed")
    for required in (
        '(fp_rect (start -1.675 -1.25) (end 1.675 1.25)',
        '(pad "" np_thru_hole circle (at 0.575 0) (size 0.6 0.6) (drill 0.6)',
        '(gr_circle (center 0 0.64) (end 0.64 0.64) (width 0.37)',
        '(keepout (tracks not_allowed) (vias not_allowed) (pads allowed) (copperpour not_allowed)',
    ):
        if required not in mic_text:
            fail(f"IM68A130 source footprint is missing {required}")


def check_active_custom_footprint_pin_sets(components, min_custom: int = 10) -> None:
    """Require every active project-local symbol pin to exist in its footprint."""
    checked: set[str] = set()
    for component in components.values():
        footprint = component.footprint or ""
        if not footprint.startswith("ducktop2:"):
            continue
        name = footprint.split(":", 1)[1]
        path = ROOT / "ducktop2.pretty" / f"{name}.kicad_mod"
        if not path.exists():
            fail(f"active custom footprint source is missing: {path.name}")
        pad_names = {pad[0] for pad in source_footprint_pads(path) if pad[0]}
        missing = sorted(pin for pin in component.pin_nets if pin and pin not in pad_names)
        if missing:
            fail(f"{component.ref} symbol pins absent from {path.name}: {missing}")
        checked.add(name)
    if len(checked) < min_custom:
        fail(f"unexpectedly few active custom footprints checked: {len(checked)}")


def check_oled(components, fps=None):
    expect_value_prefix(components, "C170", "22u 25V X7R", "E-key bulk capacitor")
    expect(prop(components, "C170", "MPN"), "GRM32ER71E226KE15L", "E-key characterized capacitor")
    cable_footprint = "Connector_JST:JST_GH_SM04B-GHS-TB_1x04-1MP_P1.25mm_Horizontal"
    for ref in ("J41", "J45"):
        expect(comp(components, ref).footprint, cable_footprint, f"{ref} cable footprint")
    expect(comp(components, "U45").footprint, "Package_SO:TSSOP-24_4.4x7.8mm_P0.65mm", "U45 footprint")
    for ref, sda, scl in [
        ("J41", "/Wi-Fi{slash}Bluetooth & OLEDs/OLED_A_SDA", "/Wi-Fi{slash}Bluetooth & OLEDs/OLED_A_SCL"),
        ("J45", "/Wi-Fi{slash}Bluetooth & OLEDs/OLED_B_SDA", "/Wi-Fi{slash}Bluetooth & OLEDs/OLED_B_SCL"),
    ]:
        expect(net(components, ref, "1"), "GND", f"{ref} pin 1")
        expect(net(components, ref, "2"), "/MCU_3V3", f"{ref} pin 2")
        expect(net(components, ref, "3"), scl, f"{ref} pin 3")
        expect(net(components, ref, "4"), sda, f"{ref} pin 4")
        expect(prop(components, ref, "MPN"), "SM04B-GHS-TB", f"{ref} PCB connector")
        expect(prop(components, ref, "MatingHousing"), "GHR-04V-S", f"{ref} cable housing")
        expect(prop(components, ref, "Contacts"), "SSHL-002T-P0.2", f"{ref} cable contacts")
        expect(prop(components, ref, "CablePinout"), "1=GND;2=3V3;3=SCL;4=SDA", f"{ref} cable map")
        if fps is not None:
            if ref not in fps:
                fail(f"{ref} missing from PCB")
            if fps[ref].footprint != cable_footprint:
                fail(f"{ref} PCB footprint is not the OLED cable connector: {fps[ref].footprint}")

    for pin in ("1", "2", "12", "21"):
        expect(net(components, "U45", pin), "GND", f"U45 pin {pin}")
    expect(net(components, "U45", "3"), "/SERVICE_MUX_RESET_N", "U45 service-mux reset")
    expect(net(components, "U45", "22"), "/I2C_SCL", "U45 upstream SCL")
    expect(net(components, "U45", "23"), "/I2C_SDA", "U45 upstream SDA")
    expect(net(components, "U45", "24"), "/MCU_3V3", "U45 VCC")
    for idx, (sda_pin, scl_pin) in enumerate((("8", "9"), ("10", "11")), start=1):
        expect(net(components, "U45", sda_pin), f"/PD{idx}_I2C_SDA", f"U45 PD{idx} downstream SDA")
        expect(net(components, "U45", scl_pin), f"/PD{idx}_I2C_SCL", f"U45 PD{idx} downstream SCL")
    for pin in ("13", "14", "15", "16", "17", "18", "19", "20"):
        expect_unconnected(components, "U45", pin)
    expect(net(components, "C185", "1"), "/MCU_3V3", "C185 pin 1")
    expect(net(components, "C185", "2"), "GND", "C185 pin 2")


def check_battery_and_charger(components):
    modern = prop(components, "U2", "MPN") == "ISL9241IRTZ"
    # Board split Phase 2.4: the pack protection contracts (J2, F1, U719
    # BQ77915, U11 LTC4368, Q11/Q12, Q703/Q704, RS10/RS11, C725, R700-R709,
    # Q701, C700/C724) moved to the BMS daughterboard (bms/bms.kicad_sch).
    # They are verified by check_bms_pack() against the bms project netlist.
    # The center keeps only the gauge (U10), charger (U2), and ship FET (Q25)
    # contracts below, plus the pack-boundary testpoints that remain here.
    expect(net(components, "RS1", "1"), "/FG_VSS", "RS1 pack-side Kelvin node (FPC-3 boundary)")
    expect(net(components, "RS1", "2"), "GND", "RS1 system side")
    for obsolete in ("NTC2", "NTC4"):
        if obsolete in components:
            fail(f"obsolete motherboard battery thermistor {obsolete} remains")

    expect(prop(components, "LED1", "Manufacturer"), "Kingbright", "charger LED manufacturer")
    expect(prop(components, "LED1", "MPN"), "APT1608SGC", "charger LED exact MPN")

    for ref, want in {
        "TP1": "GND",
        "TP2": "/PACK_POS_FUSED",
        "TP3": "/VSYS",
        "TP4": "/EC_AON_IN",
        "TP7": "/MCU_3V3",
        "TP9": "/CHG_INT_N",
        "TP10": "/PACK_FAULT_N",
        "TP11": "/AON_FAULT_N",
    }.items():
        expect(comp(components, ref).footprint,
               "TestPoint:TestPoint_Pad_D1.0mm", f"{ref} fixture footprint")
        expect(net(components, ref, "1"), want, f"{ref} fixture net")
        expect(prop(components, ref, "ProcurementClass"),
               "PCB copper test feature", f"{ref} procurement class")
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
