EwoudVV/ducktop2/gen/check_center_pcie_coupling.py

#!/usr/bin/env python3
"""Check the center board's differential routing without changing the board."""
from pathlib import Path
import argparse,hashlib,json,math,os,shutil,subprocess,sys,collections
DEPENDENCY_ERROR=None
try:
 import numpy as np
 from shapely.geometry import LineString,Polygon,Point,box
 from shapely.ops import unary_union
 import shapely
except ImportError as error:
 DEPENDENCY_ERROR=str(error)
ROOT=Path(__file__).resolve().parents[1]
def cross(a,b):return float(a[0]*b[1]-a[1]*b[0])
def polygon(r):return Polygon(r['polygon_mm']) if 'polygon_mm' in r else box(*r['bounds_mm'])
def automatic_corners(tracks,nominal,tolerance,gaps_by_layer=None):
 result=[]
 for net in sorted({v['net'] for v in tracks}):
  stem=net[:-2];opp=stem+('_N' if net.endswith('_P') else '_P')
  for layer in sorted({t['layers'][0] for t in tracks if t['net']==net}):
   layer_nominal=(gaps_by_layer or {}).get(layer,nominal)
   own=[t for t in tracks if t['net']==net and t['layers']==[layer]];others=[t for t in tracks if t['net']==opp and t['layers']==[layer]];joints=collections.defaultdict(list)
   for t in own:
    for end,other in [(t['start'],t['end']),(t['end'],t['start'])]:joints[tuple(end)].append((t,np.asarray(other)-end))
   for at,joined in joints.items():
    if len(joined)!=2 or any(np.linalg.norm(v)<1e-10 for _,v in joined):continue
    directions=[v/np.linalg.norm(v) for _,v in joined]
    bend=math.pi-math.acos(max(-1.,min(1.,float(np.dot(*directions)))))
    if bend<1e-5 or bend>math.pi/2+2e-5:continue
    matching=[]
    for t,u in joined:
     uu=u/np.linalg.norm(u);valid=[]
     for n in others:
      vv=np.asarray(n['end'])-n['start'];vv=vv/np.linalg.norm(vv)
      if abs(cross(uu,vv))>2e-5:continue
      gap=abs(cross(uu,np.asarray(n['start'])-at))-(t['width']+n['width'])/2
      # Reject remote parallel lines: matching projection must reach this
      # corner neighborhood, not merely lie on the same infinite line.
      if abs(gap-layer_nominal)<=tolerance and LineString([n['start'],n['end']]).distance(Point(at))<2*(layer_nominal+t['width']):valid.append({'id':n['id'],'gap_mm':gap})
     matching.append(valid)
    if not all(matching):continue
    width=joined[0][0]['width'];pitch=layer_nominal+width;radius=pitch*math.tan(bend/2)+.008
    result.append({'name':f'paired corner {net} {at[0]:.6f},{at[1]:.6f}','category':'paired_corner','stem':stem,'layer':layer,'bounds_mm':[at[0]-radius,at[1]-radius,at[0]+radius,at[1]+radius],'own_tracks':[t['id'] for t,_ in joined],'matching_parallel_tracks':matching,'bend_degrees':math.degrees(bend),'max_nearest_gap_mm':pitch/math.cos(bend/2)-width+.00001,'max_total_length_mm':{'P':4*radius,'N':4*radius},'max_uncoupled_length_mm':{'P':4*radius,'N':4*radius},'automatic_corner_radius_mm':radius})
 return result

def measure_max(part,width,others,step):
 if not others:return float('inf'),float('inf')
 n=max(1,math.ceil(part.length/step));coords=np.asarray([part.interpolate((i+.5)*part.length/n).coords[0] for i in range(n)]);points=shapely.points(coords)
 bywidth=collections.defaultdict(list)
 for t in others:bywidth[t['width']].append(LineString([t['start'],t['end']]))
 gaps=np.full(n,np.inf)
 for w,lines in bywidth.items():gaps=np.minimum(gaps,shapely.distance(points,unary_union(lines))-(width+w)/2)
 sampled=float(gaps.max());return sampled,sampled+part.length/n/2

def check(data,spec):
 names={net:p['stem']+'_'+pol for p in spec['pairs'] for pol,net in p.get('nets',{}).items()}
 if names:data=dict(data,items=[dict(v,net=names.get(v['net'],v['net'])) for v in data['items']])
 from center_pcie_geometry import Curve,merge as curve_merge,complement,intersection,gap_measure
 assert spec['schema_version']==1;stems={v['stem'] for v in spec['pairs']};items=[v for v in data['items'] if v['net'][:-2] in stems];tracks=[v for v in items if v['type'] in ('PCB_TRACK','PCB_ARC')];errors=[];curves={}
 for t in tracks:
  try:curves[t['id']]=Curve(t)
  except (ValueError,KeyError,np.linalg.LinAlgError) as error:errors.append({'kind':'invalid_curve','id':t['id'],'reason':str(error)})
 if len(curves)!=len(tracks):return {'status':'failed','candidate_sha256':data['source_sha256'],'scope':spec['scope'],'blocking_findings':errors,'outside_region_uncoupled':[],'region_measurements':[],'minimum_gaps':[]}
 nominal_default=spec['nominal_gap_mm'];gaps_by_layer=spec.get('nominal_gap_by_layer_mm',{})
 allowed_layers={layer for pair in spec['pairs'] for layer in pair['widths_by_layer']}
 if not isinstance(gaps_by_layer,dict) or any(layer not in allowed_layers or type(gap) not in (int,float) or not math.isfinite(gap) or gap<=0 for layer,gap in gaps_by_layer.items()):raise ValueError('layer gaps must be positive finite numbers on allowed signal layers')
 tol=spec['maximum_rounding_tolerance_mm'];regions=list(spec['regions']);corners=automatic_corners([t for t in tracks if t['type']=='PCB_TRACK'],nominal_default,spec['paired_corner_leg_tolerance_mm'],gaps_by_layer);regions+=corners
 region_names=[r['name'] for r in regions]
 if len(region_names)!=len(set(region_names)):raise ValueError('explicit regions and inferred corners must have unique names')
 automatic_names={r['name'] for r in corners}
 bystem={v['stem']:v for v in spec['pairs']};summaries={r['name']:{'P':{'length_mm':0.,'uncoupled_length_mm':0.},'N':{'length_mm':0.,'uncoupled_length_mm':0.},'maximum_nearest_gap_sample_mm':0.,'maximum_nearest_gap_upper_bound_mm':0.} for r in regions};outside=[];minimums=[]
 for stem in sorted(stems):
  allowed=bystem[stem]['widths_by_layer']
  for pol in ['P','N']:
   if not any(t['net']==stem+'_'+pol for t in tracks):errors.append({'kind':'missing_polarity','net':stem+'_'+pol})
  for t in tracks:
   if t['net'][:-2]!=stem:continue
   if len(t['layers'])!=1 or t['layers'][0] not in allowed or min(abs(t['width']-x) for x in allowed.get(t['layers'][0],[float('inf')]))>.000001:errors.append({'kind':'width_or_layer','id':t['id'],'net':t['net'],'layers':t['layers'],'width':t['width']})
  for layer in sorted({t['layers'][0] for t in tracks if t['net'][:-2]==stem}):
   nominal=gaps_by_layer.get(layer,nominal_default)
   rs=[r for r in regions if r['stem']==stem and r['layer']==layer];both={pol:[curves[t['id']] for t in tracks if t['net']==stem+'_'+pol and t['layers']==[layer]] for pol in ['P','N']};minimum_count=0
   for a in both['P']:
    for b in both['N']:
     close=a.capsule_coverage(b,nominal-spec['paired_corner_leg_tolerance_mm']-a.rounding_uncertainty-b.rounding_uncertainty+(a.width+b.width)/2)
     if sum(high-low for low,high in close)*a.length>spec['outside_uncoupled_rounding_length_mm']:
      errors.append({'kind':'minimum_gap','stem':stem,'layer':layer,'items':[a.item['id'],b.item['id']],'below_minimum_length_mm':sum(high-low for low,high in close)*a.length});minimum_count+=1
   minimums.append({'stem':stem,'layer':layer,'minimum_gap_floor_mm':nominal-spec['paired_corner_leg_tolerance_mm'],'below_minimum_pairs':minimum_count,'method':'exact line/circular-arc capsule intersections'})
   for pol,opp in [('P','N'),('N','P')]:
    others=both[opp]
    for curve in both[pol]:
     coverage=[]
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
